me-processware/powdersense/data/powdersense_2.png

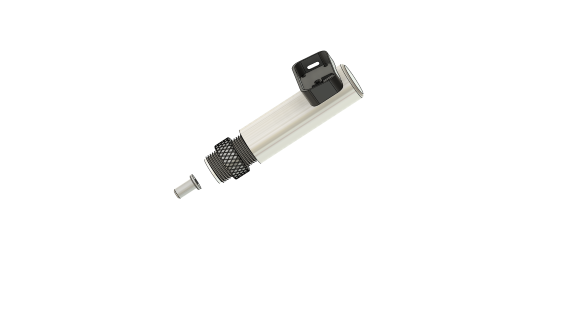
data/powdersense_2.png
