me-processware/powdersense/docs/images/bourns_potentiometer.png

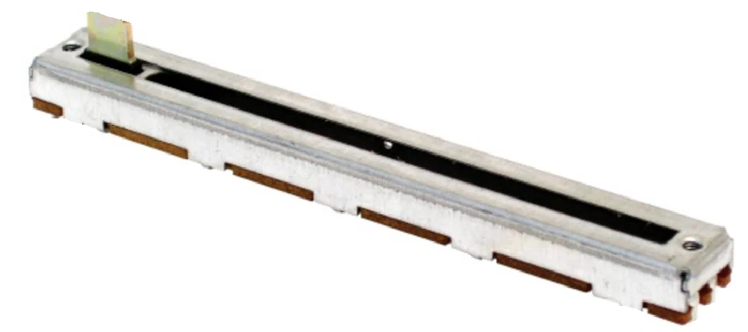
docs/images/bourns_potentiometer.png
