me-processware/powdersense/docs/images/product_photo.png

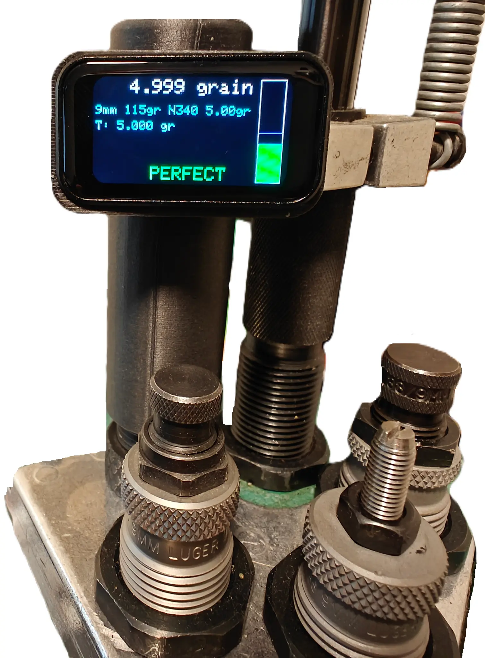
docs/images/product_photo.png
