me-processware/powdersense/docs/images/product_render.png

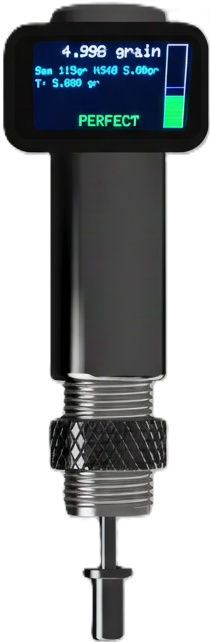
docs/images/product_render.png
