me-processware/powdersense/docs/screenshots/dashboard_advanced.webp

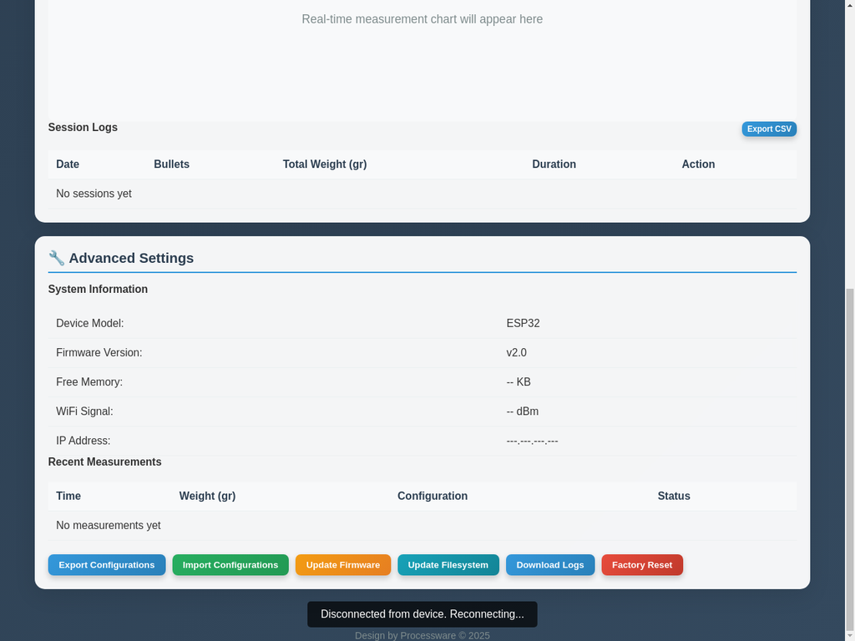
docs/screenshots/dashboard_advanced.webp
