me-processware/powdersense/docs/screenshots/dashboard_main.webp

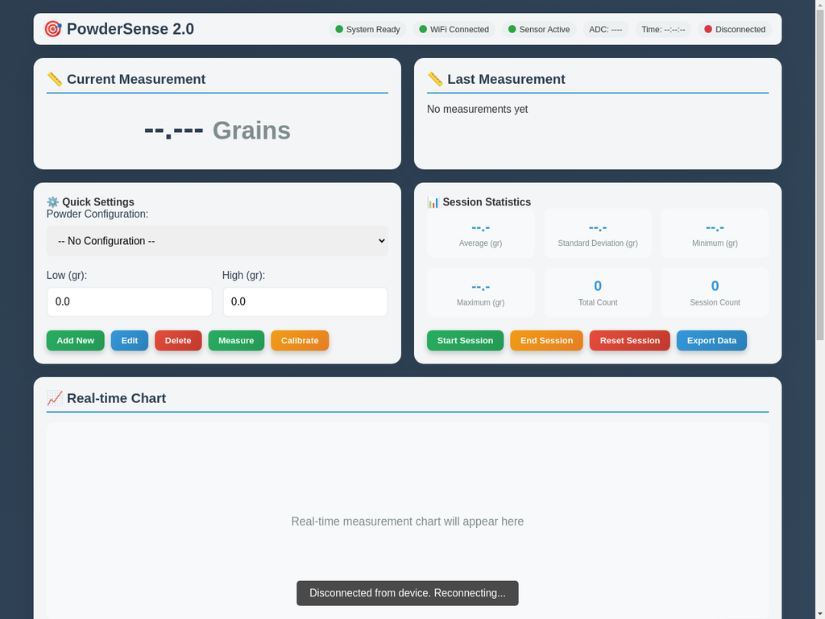
docs/screenshots/dashboard_main.webp
