me-processware/powdersense/docs/screenshots/profile_dialog.webp

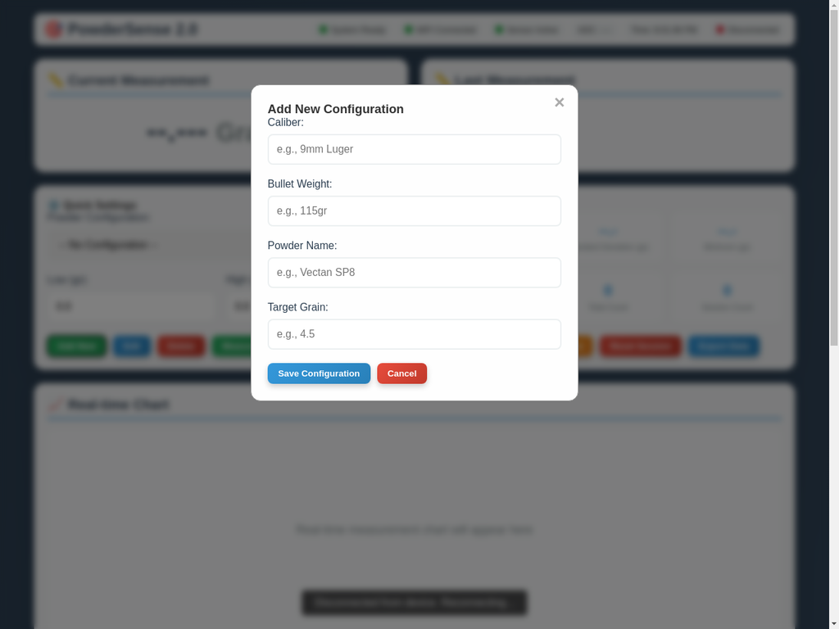
docs/screenshots/profile_dialog.webp
