me-processware/powdersense/docs/screenshots/wifi_config.webp

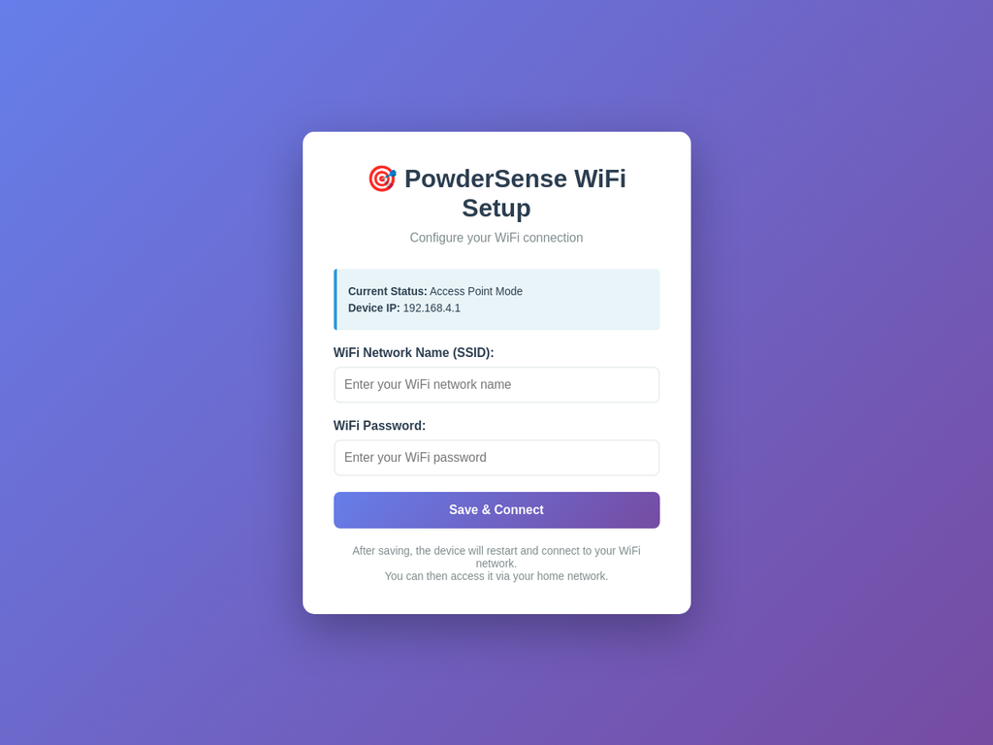
docs/screenshots/wifi_config.webp
