me-processware/powdersense/docs/images/assembly/step_08.jpg

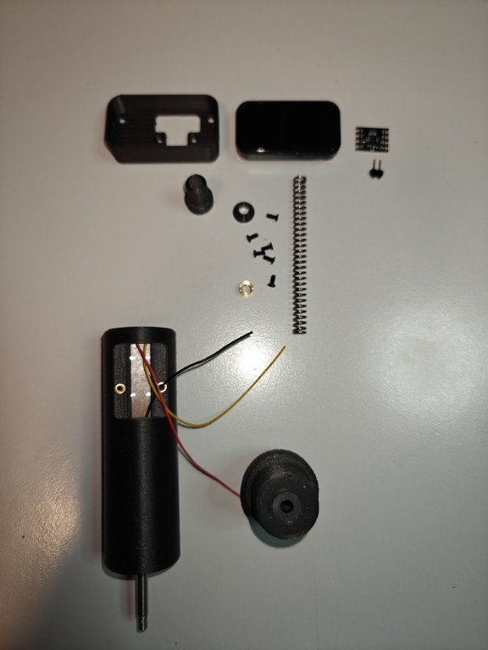
docs/images/assembly/step_08.jpg
